urmel79/IO_esp8266_oled_gps_lora_gh/node-red_ttn/node-red_flow_ttn2map.png

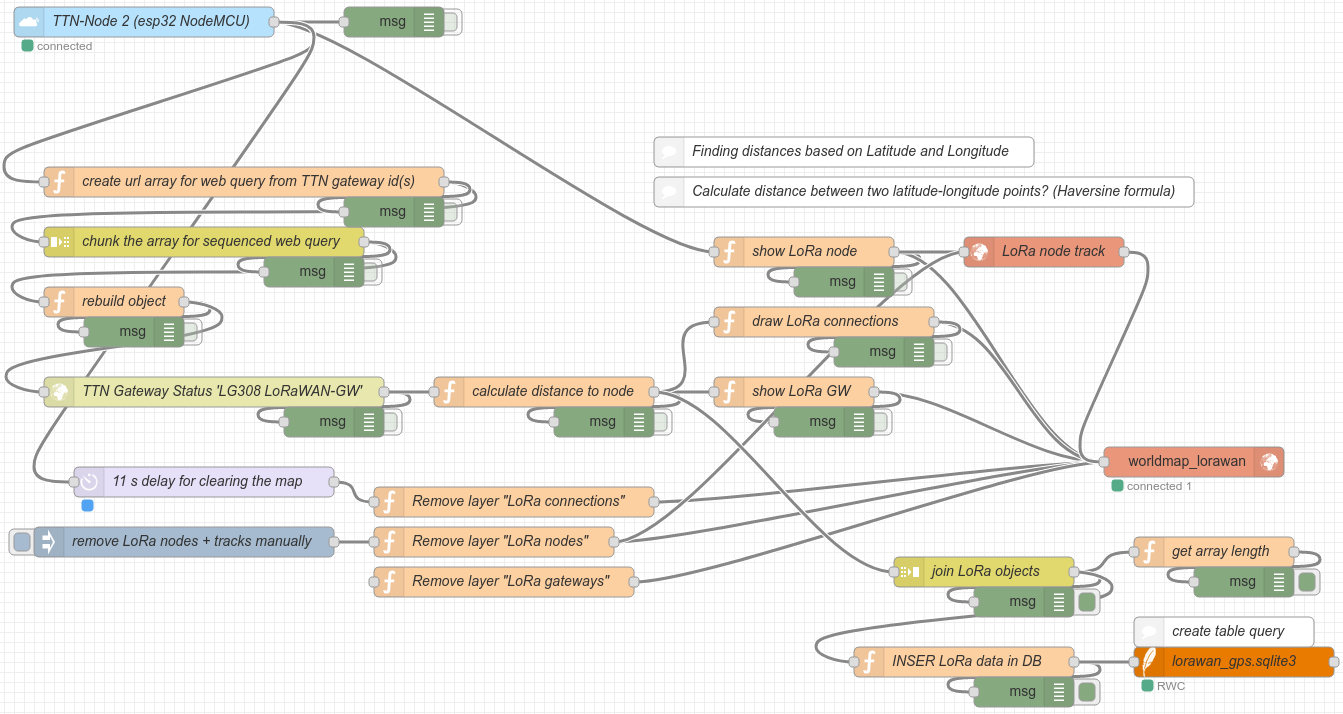
node-red_ttn/node-red_flow_ttn2map.png
