urmel79/IO_esp8266_oled_gps_lora_gh/node-red_ttn/phpLiteAdmin_db_lorawan_gps_c.png

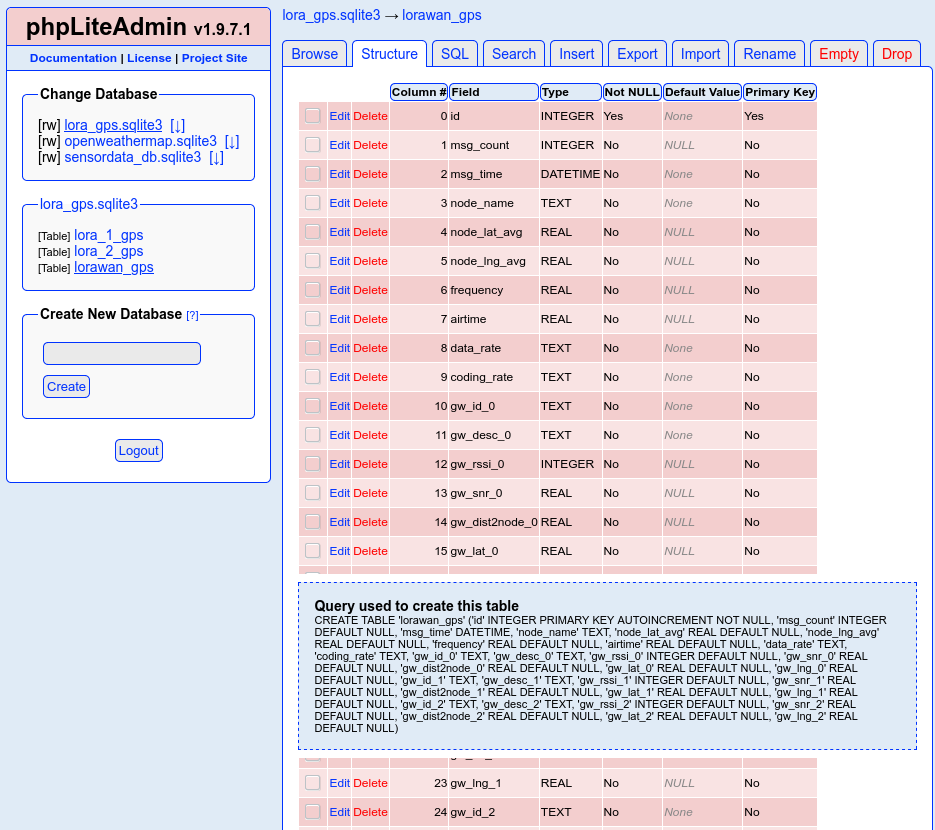
node-red_ttn/phpLiteAdmin_db_lorawan_gps_c.png
