urmel79/IO_esp8266_oled_gps_lora_gh/src/function_gps.cpp

#include "function_gps.hpp"

// includes implicit <sys/types.h> (necessary for SoftwareSerial)
// otherwise errors like 'ssize_t' does not name a type'
#include <Arduino.h>

// Install EspSoftwareSerial by Peter Lerup
// Implementation of the Arduino software serial for ESP8266/ESP32.
// Important: v5.0.4 is the latest version what compiles without errors
// (current versions spill massive errors, maybe about interrupt handling?)
// Update: v5.3.4 does compile again without errors (@TODO: integration test pending)
//          => does not compile in other projects => why? => so going back to v5.0.4
// Update to EspSoftwareSerial v6.4.0 (latest): API of begin() function has changed and no return value any more
#include <SoftwareSerial.h> //Included SoftwareSerial Library

#define GPS_BAUD_RATE 9600

// Install RunningAverage by Rob Tillaart
// The library stores the last N individual values in a circular buffer to calculate the running average.
// https://github.com/RobTillaart/Arduino/tree/master/libraries/RunningAverage
// #include "RunningAverage.h"
// use rewritten RunningAverage library (revert back  from float to double),
// because for smoothing GPS values I need much higher precision ...
#include "function_runningAverage_double.hpp"

#define GPS_AVG_FILTER_SIZE 10

RunningAverage gps_RunningAVG_lat(GPS_AVG_FILTER_SIZE);  // RunningAverage object for gps latitude
RunningAverage gps_RunningAVG_lng(GPS_AVG_FILTER_SIZE);  // RunningAverage object for gps longitude
RunningAverage gps_RunningAVG_alt(GPS_AVG_FILTER_SIZE);  // RunningAverage object for gps altitude

bool g_b_init_RunningAverage_values = false;

// Important: initial value has to be 'true'!
bool g_b_enableRx = true;

struct_gps_RunningAVG_Median g_avg;

// #####################
// @TODO:
//        comparison between RunningAverage and RunningMedian => not so susceptible to outliers?
//        => library has to be rewritten first (revert back  from float to double)
// #####################
// RunningMedian by Rob Tillaart
// The library stores the last N individual values in a buffer to select the median. It filters outliers.
// https://github.com/RobTillaart/Arduino/tree/master/libraries/RunningMedian
// #include "RunningMedian.h"
// use rewritten RunningMedian library (revert back  from float to double),
// because for smoothing GPS values I need much higher precision ...
#include "function_runningMedian_double.hpp"

#if defined(GPS_AVG_FILTER_SIZE) && ( GPS_AVG_FILTER_SIZE % 2 == 0 )
  #define GPS_MED_FILTER_SIZE GPS_AVG_FILTER_SIZE
#else
  #define GPS_MED_FILTER_SIZE GPS_AVG_FILTER_SIZE+1
#endif

RunningMedian gps_RunningMedian_lat(GPS_MED_FILTER_SIZE);  // RunningMedian object for gps latitude
RunningMedian gps_RunningMedian_lng(GPS_MED_FILTER_SIZE);  // RunningMedian object for gps longitude
RunningMedian gps_RunningMedian_alt(GPS_MED_FILTER_SIZE);  // RunningMedian object for gps altitude

// #if !defined(D5)
//   #define D3 (0)
//   #define D4 (2)
//
//   #define D5 (14)
//   #define D6 (12)
//
//   // if D8 ist connected to TxD during boot, there will be errors
//   // => better use D5+D6 for serial
//   #define D7 (13)
//   #define D8 (15)
// #endif

// Started SoftwareSerial at RX and TX pin of ESP8266/NodeMCU
// Some arduino boards only have one hardware serial port, so a software serial port is needed instead.
// comment out the above definition and uncomment these lines
// SoftwareSerial serial_gps(D3, D4); // RxD: GPIO0 (D3), TxD: GPIO2 (D4)
SoftwareSerial serial_gps;

// The TinyGPS++ object
// Examples:
// https://github.com/mkconer/ESP8266_GPS/blob/master/ESP8266_GPS_OLED_Youtube.ino
// https://circuitdigest.com/microcontroller-projects/interfacing-gps-with-nodemcu-esp12
TinyGPSPlus gps;

void initSS_gps() {
  serial_gps.begin(GPS_BAUD_RATE, SWSERIAL_8N1, RxD_Pin, TxD_Pin, false, 95, 11);

  gps_RunningAVG_lat.clear(); // explicitly start with a clean RunningAverage object
  gps_RunningAVG_lng.clear(); // explicitly start with a clean RunningAverage object
  gps_RunningAVG_alt.clear(); // explicitly start with a clean RunningAverage object

  gps_RunningMedian_lat.clear(); // explicitly start with a clean RunningMedian object
  gps_RunningMedian_lng.clear(); // explicitly start with a clean RunningMedian object
  gps_RunningMedian_alt.clear(); // explicitly start with a clean RunningMedian object

  // initialize the RunningAverage arrays with appropriate starting values (e. g. first raw value)
  g_b_init_RunningAverage_values = true;
}

// is called in every loop cycle => polling the serial line
TinyGPSPlus read_gps() {

  // TinyGPSPlus l_gps_values;

  // // Only for debugging the gps:
  // // while there is data coming in, read it
  // // and send to the hardware serial port:
  // while (serial_gps.available() > 0) {
  // 	Serial.write(serial_gps.read());
  // 	yield();
  // }

  // This sketch displays information every time a new sentence is correctly encoded.
  while (serial_gps.available() > 0) {
  // while (1) {

    gps.encode(serial_gps.read());

    if (gps.location.isValid()) {

      // l_gps_values.location.lat = gps.location.lat();
      // l_gps_values.location.lng = gps.location.lng();
      // g_gps_values.date = gps.date;
      // g_gps_values.time = gps.time;
      // g_gps_values.speed = gps.speed;
      // g_gps_values.course = gps.course;
      // g_gps_values.altitude = gps.altitude;
      // g_gps_values.satellites = gps.satellites;
      // g_gps_values.hdop = gps.hdop;

      // make a local (shallow) copy of gps structure, just like with memcpy.
      // That means if you have e.g. a structure containing pointers, it's only the actual
      // pointers that will be copied and not what they point to, so after the copy you
      // will have two pointers pointing to the same memory.
      // l_gps_values = gps;

      // gps_RunningAVG_lat.addValue(gps.location.lat());
      // gps_RunningAVG_lng.addValue(gps.location.lng());

      // gps_RunningAVG_lat.addValue(gps.location.lat());
      // gps_RunningAVG_lng.addValue(gps.location.lng());
      //
      // gps_RunningMedian_lat.addValue(gps.location.lat());
      // gps_RunningMedian_lng.addValue(gps.location.lng());

      return gps;
    }

    // Yielding
    // This is one of the most critical differences between the ESP8266 and a more classical
    // Arduino microcontroller. The ESP8266 runs a lot of utility functions in the background –
    // keeping WiFi connected, managing the TCP/IP stack, and performing other duties.
    // Blocking these functions from running can cause the ESP8266 to crash and reset itself.
    // To avoid these mysterious resets, avoid long, blocking loops in your sketch.
    //
    // The amazing creators of the ESP8266 Arduino libraries also implemented a yield() function,
    // which calls on the background functions to allow them to do their things.
    yield();
  }

  return gps;
  // return l_gps_values;
}

// is called every 2 seconds in main loop
void gps_RunningAVG_Median_addValues() {
  if ( g_b_init_RunningAverage_values ) {
    // fill the average and median buffer with a starting value
    // the param number determines how often value is added (weight)
    // number should preferably be between 1 and size
    gps_RunningAVG_lat.fillValue(gps.location.lat(), GPS_AVG_FILTER_SIZE); // GPS_AVG_FILTER_SIZE
    gps_RunningAVG_lng.fillValue(gps.location.lng(), GPS_AVG_FILTER_SIZE); // GPS_AVG_FILTER_SIZE
    gps_RunningAVG_alt.fillValue(gps.altitude.meters(), GPS_AVG_FILTER_SIZE); // GPS_AVG_FILTER_SIZE

    gps_RunningMedian_lat.fillValue(gps.location.lat(), GPS_MED_FILTER_SIZE); // GPS_MED_FILTER_SIZE
    gps_RunningMedian_lng.fillValue(gps.location.lng(), GPS_MED_FILTER_SIZE); // GPS_MED_FILTER_SIZE
    gps_RunningMedian_alt.fillValue(gps.altitude.meters(), GPS_MED_FILTER_SIZE); // GPS_MED_FILTER_SIZE

    // gps_RunningAVG_lat.fillValue(51.003935333, GPS_AVG_FILTER_SIZE); // GPS_AVG_FILTER_SIZE
    // gps_RunningAVG_lng.fillValue(13.686355833, GPS_AVG_FILTER_SIZE); // GPS_AVG_FILTER_SIZE

    g_b_init_RunningAverage_values = false;
  }
  else {
    gps_RunningAVG_lat.addValue(gps.location.lat());
    gps_RunningAVG_lng.addValue(gps.location.lng());
    gps_RunningAVG_alt.addValue(gps.altitude.meters());

    gps_RunningMedian_lat.addValue(gps.location.lat());
    gps_RunningMedian_lng.addValue(gps.location.lng());
    gps_RunningMedian_alt.addValue(gps.altitude.meters());
  }
}

// is called every 2 seconds in main loop
struct_gps_RunningAVG_Median get_gps_RunningAVG_Median() {
  // struct_gps_RunningAVG_Median l_avg;

  g_avg.gps_RunningAVG_lat = gps_RunningAVG_lat.getAverage();
  g_avg.gps_RunningAVG_lng = gps_RunningAVG_lng.getAverage();
  g_avg.gps_RunningAVG_alt = gps_RunningAVG_alt.getAverage();

  g_avg.gps_RunningMedian_lat = gps_RunningMedian_lat.getMedian();
  g_avg.gps_RunningMedian_lng = gps_RunningMedian_lng.getMedian();
  g_avg.gps_RunningMedian_alt = gps_RunningMedian_alt.getMedian();

  g_avg.gps_RunningAVG_lat_size = gps_RunningAVG_lat.getSize();
  g_avg.gps_RunningAVG_lng_size = gps_RunningAVG_lng.getSize();
  g_avg.gps_RunningAVG_alt_size = gps_RunningAVG_alt.getSize();

  g_avg.gps_RunningAVG_lat_cnt = gps_RunningAVG_lat.getCount();
  g_avg.gps_RunningAVG_lng_cnt = gps_RunningAVG_lng.getCount();
  g_avg.gps_RunningAVG_alt_cnt = gps_RunningAVG_alt.getCount();

  return g_avg;
}

// Rx interrupts are conflicting with OTA updates => disable serial Rx!
void function_gps_disable_Rx( void ) {
  // if deactivated, return asap
  if ( !g_b_enableRx ) return;

  // Disable interrupts on the rx pin
  serial_gps.enableRx(false);
  g_b_enableRx = false;
  Serial.println("[GPS] disable Rx because of conflicting interrupts.");
}

void function_gps_enable_Rx( void ) {
  // if activated, return asap
  if ( g_b_enableRx ) return;

  // Enable interrupts on the rx pin after wifi reconnect
  serial_gps.enableRx(true);
  g_b_enableRx = true;
  Serial.println("[GPS] enable Rx again.");
}






//
