urmel79/IO_esp8266_oled_gps_lora_gh/src/function_runningAverage_double.cpp

//
//    FILE: function_runningAverage_double.cpp
//  AUTHOR: Rob.Tillaart@gmail.com + Bjoern Kasper
// VERSION: 0.2.13 => 0.2.13d
//    DATE: 2016-dec-01 => 2020-jan-05
// PURPOSE: RunningAverage library for Arduino
//
// The library stores N individual values in a circular buffer,
// to calculate the running average.
//
// HISTORY:
// 0.1.00 - 2011-01-30 initial version
// 0.1.01 - 2011-02-28 fixed missing destructor in .h
// 0.2.00 - 2012-??-?? Yuval Naveh added trimValue (found on web)
//          http://stromputer.googlecode.com/svn-history/r74/trunk/Arduino/Libraries/RunningAverage/RunningAverage.cpp
// 0.2.01 - 2012-11-21 refactored
// 0.2.02 - 2012-12-30 refactored trimValue -> fillValue
// 0.2.03 - 2013-11-31 getElement
// 0.2.04 - 2014-07-03 added memory protection
// 0.2.05 - 2014-12-16 changed float -> double
// 0.2.06 - 2015-03-07 all size uint8_t
// 0.2.07 - 2015-03-16 added getMin() and getMax() functions (Eric Mulder)
// 0.2.08 - 2015-04-10 refactored getMin() and getMax() implementation
// 0.2.09 - 2015-07-12 refactor const + constructor
// 0.2.10 - 2015-09-01 added getFastAverage() and refactored getAverage()
//                     http://forum.arduino.cc/index.php?topic=50473
// 0.2.11 - 2015-09-04 added getMaxInBuffer() getMinInBuffer() request (Antoon)
// 0.2.12 - 2016-12-01 added GetStandardDeviation() GetStandardError() BufferIsFull()  (V0v1kkk)
// 0.2.13 - 2017-07-26 revert double to float - issue #33;
//                     refactored a bit; marked some TODO's; all function names to camelCase
// 0.2.13d - 2020-01-05 BK: revert back  from float to double
//                          for smoothing GPS values I need much higher precision
//                          in comparison to Arduino, the ESP8266/ESP32 boards have
//                          different size of float vs. double (4 byte vs. 8 byte)
//
// Released to the public domain
//

#include "function_runningAverage_double.hpp"

#include <stdlib.h>
#include <math.h>


RunningAverage::RunningAverage(const uint8_t size)
{
  _size = size;
  _ar = (double*) malloc(_size * sizeof(double));
  if (_ar == NULL) _size = 0;
  clear();
}

RunningAverage::~RunningAverage()
{
  if (_ar != NULL) free(_ar);
}

// resets all counters
void RunningAverage::clear()
{
  _cnt = 0;
  _idx = 0;
  _sum = 0.0;
  _min = NAN;
  _max = NAN;
  for (uint8_t i = 0; i < _size; i++)
  {
    _ar[i] = 0.0; // keeps addValue simpler
  }
}

// adds a new value to the data-set
void RunningAverage::addValue(const double value)
{
  if (_ar == NULL) return;  // allocation error

  _sum -= _ar[_idx];
  _ar[_idx] = value;
  _sum += _ar[_idx];
  _idx++;

  if (_idx == _size) _idx = 0;  // faster than %

  // handle min max
  if (_cnt == 0) _min = _max = value;
  else if (value < _min) _min = value;
  else if (value > _max) _max = value;

  // update count as last otherwise if ( _cnt == 0) above will fail
  if (_cnt < _size) _cnt++;
}

// returns the average of the data-set added sofar
double RunningAverage::getAverage() const
{
  if (_cnt == 0) return NAN;

  double sum = 0;
  for (uint8_t i = 0; i < _cnt; i++)
  {
    sum += _ar[i];
  }
  return sum / _cnt;
}

double RunningAverage::getFastAverage() const
{
  if (_cnt == 0) return NAN;

  return _sum / _cnt;
}

// returns the minimum value in the buffer
double RunningAverage::getMinInBuffer() const
{
  if (_cnt == 0) return NAN;

  double min = _ar[0];
  for (uint8_t i = 1; i < _cnt; i++)
  {
    if (_ar[i] < min) min = _ar[i];
  }
  return min;
}

// returns the maximum value in the buffer
double RunningAverage::getMaxInBuffer() const
{
  if (_cnt == 0) return NAN;

  double max = _ar[0];
  for (uint8_t i = 1; i < _cnt; i++)
  {
    if (_ar[i] > max) max = _ar[i];
  }
  return max;
}


// returns the value of an element if exist, NAN otherwise
double RunningAverage::getElement(uint8_t idx) const
{
  if (idx >=_cnt ) return NAN;

  return _ar[idx];
}

// Return standard deviation of running average. If buffer is empty, return NAN.
double RunningAverage::getStandardDeviation() const
{
  if (_cnt == 0) return NAN;

  double temp = 0;
  double average = getFastAverage();
  for (uint8_t i = 0; i < _cnt; i++)
  {
    temp += pow((_ar[i] - average), 2);
  }
  temp = sqrt(temp/(_cnt - 1));     // TODO possible divide by zero ....

  return temp;
}

// Return standard error of running average. If buffer is empty, return NAN.
double RunningAverage::getStandardError() const //++
{
  double temp = getStandardDeviation();

  if (temp == NAN) return NAN;

  double n;
  if (_cnt >= 30) n = _cnt;
  else n = _cnt - 1;                // TODO fails if _cnt == 0
  temp = temp/sqrt(n);              // TODO fails if _cnt == 1

  return temp;
}

// fill the average with a value
// the param number determines how often value is added (weight)
// number should preferably be between 1 and size
void RunningAverage::fillValue(const double value, const uint8_t number)
{
  clear(); // TODO conditional?  if (clr) clear();

  for (uint8_t i = 0; i < number; i++)
  {
    addValue(value);
  }
}
// END OF FILE
