urmel79/IO_esp8266_oled_gps_lora_gh/src/function_runningMedian_double.hpp

//
//    FILE: function_runningMedian_double.h
//  AUTHOR: Rob.Tillaart@gmail.com + Bjoern Kasper
//    DATE: 2020-jan-06
// PURPOSE: RunningMedian library for Arduino
// VERSION: 0.1.15 => 0.1.15d
//     URL: http://arduino.cc/playground/Main/RunningMedian
// HISTORY: See RunningMedian.cpp
//
// Released to the public domain
//

#ifndef function_runningMedian_double_hpp
#define function_runningMedian_double_hpp

#if defined(ARDUINO) && ARDUINO >= 100
#include <Arduino.h>
#else
#include <WProgram.h>
#endif

#include <inttypes.h>

#define RUNNING_MEDIAN_VERSION "0.1.15"

// prepare for dynamic version
// not tested use at own risk :)
// #define RUNNING_MEDIAN_USE_MALLOC

// conditional compile to minimize lib
// by removeing a lot of functions.
#ifndef RUNNING_MEDIAN_ALL
#define RUNNING_MEDIAN_ALL
#endif


// should at least be 5 to be practical
// odd size results in a 'real' middle element.
// even size takes the lower of the two middle elements
#ifndef MEDIAN_MIN_SIZE
#define MEDIAN_MIN_SIZE     1
#endif
#ifndef MEDIAN_MAX_SIZE
#define MEDIAN_MAX_SIZE     19          // adjust if needed
#endif


class RunningMedian
{
public:
  explicit RunningMedian(const uint8_t size);  // # elements in the internal buffer
  ~RunningMedian();                            // destructor

  void clear();                        // resets internal buffer and var
  void addValue(const double value);   // adds a new value to internal buffer, optionally replacing the oldest element.
  void fillValue(const double, const uint8_t); // fill the median with a value
  double getMedian();                  // returns the median == middle element

#ifdef RUNNING_MEDIAN_ALL
  double getAverage();                 // returns average of the values in the internal buffer
  double getAverage(uint8_t nMedian);  // returns average of the middle nMedian values, removes noise from outliers
  double getHighest() { return getSortedElement(_cnt - 1); };
  double getLowest()  { return getSortedElement(0); };

  double getElement(const uint8_t n);        // get n'th element from the values in time order
  double getSortedElement(const uint8_t n);  // get n'th element from the values in size order
  double predict(const uint8_t n);           // predict the max change of median after n additions

  uint8_t getSize() { return _size; };  // returns size of internal buffer
  uint8_t getCount() { return _cnt; };  // returns current used elements, getCount() <= getSize()
#endif

protected:
  boolean _sorted;
  uint8_t _size;
  uint8_t _cnt;
  uint8_t _idx;

#ifdef RUNNING_MEDIAN_USE_MALLOC
  double * _ar;
  uint8_t * _p;
#else
  double _ar[MEDIAN_MAX_SIZE];
  uint8_t _p[MEDIAN_MAX_SIZE];
#endif
  void sort();
};

#endif  // function_runningMedian_double_hpp
// END OF FILE
