urmel79/IO_esp8266_oled_gps_lora_gh/src/function_gps.hpp

#ifndef function_gps_hpp
#define function_gps_hpp

// install path: ~/.platformio/lib/TinyGPSPlus_ID1655/
#include <TinyGPS++.h>

#if defined(NODE_MCU_LORA_1) || defined(NODE_MCU_LORA_2)
  const int RxD_Pin = D3;   // RxD: GPIO0 (D3) => TxD of GPS
  const int TxD_Pin = D4;   // TxD: GPIO2 (D4) => RxD of GPS
#elif defined(NODE_MCU_LORA_2_ESP32)
  const int RxD_Pin = 25;   // RxD: GPIO25 => TxD of GPS
  const int TxD_Pin = 26;   // TxD: GPIO26 => RxD of GPS
#endif

struct struct_gps_RunningAVG_Median {
  float gps_RunningAVG_lat;
  float gps_RunningAVG_lng;
  float gps_RunningAVG_alt;

  float gps_RunningMedian_lat;
  float gps_RunningMedian_lng;
  float gps_RunningMedian_alt;

  uint8_t gps_RunningAVG_lat_size;
  uint8_t gps_RunningAVG_lng_size;
  uint8_t gps_RunningAVG_alt_size;
  uint8_t gps_RunningAVG_lat_cnt;
  uint8_t gps_RunningAVG_lng_cnt;
  uint8_t gps_RunningAVG_alt_cnt;
};

void initSS_gps();

// Rx interrupts are conflicting with OTA updates => disable/enable serial Rx!
void function_gps_disable_Rx( void );
void function_gps_enable_Rx( void );

TinyGPSPlus read_gps();

void gps_RunningAVG_Median_addValues();
struct_gps_RunningAVG_Median get_gps_RunningAVG_Median();

#endif // function_gps_hpp
