urmel79/IO_esp8266_oled_gps_lora_gh/src/.bak/function_lora_rh.hpp

#ifndef function_lora_rh_hpp
#define function_lora_rh_hpp

#include "config.hpp"

#include <Ticker.h>

void function_lora_setup( void );

void function_lora_sendtoWait( void );

// void rf95_manager_receive( void );






















#endif // function_lora_rh_hpp
